liveboxandy/ZX-Interface-1-Replacement-ROM/Pictures/Original ROM Pins.jpg

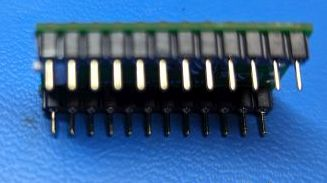
Pictures/Original ROM Pins.jpg
