liveboxandy/ZX-Interface-1-Replacement-ROM/Pictures/Programming.jpg

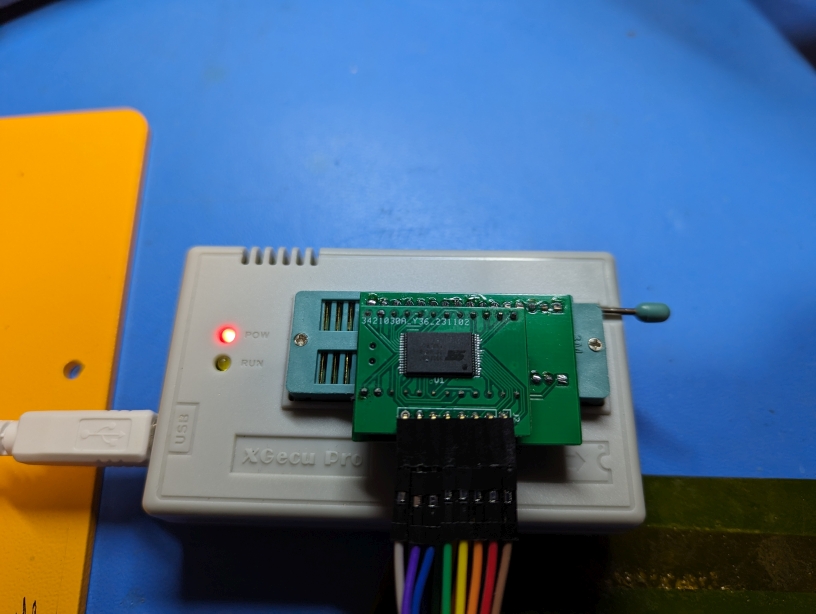
Pictures/Programming.jpg
