liveboxandy/ZX-Interface-1-Replacement-ROM/Pictures/ROM Bottom Offset.jpg

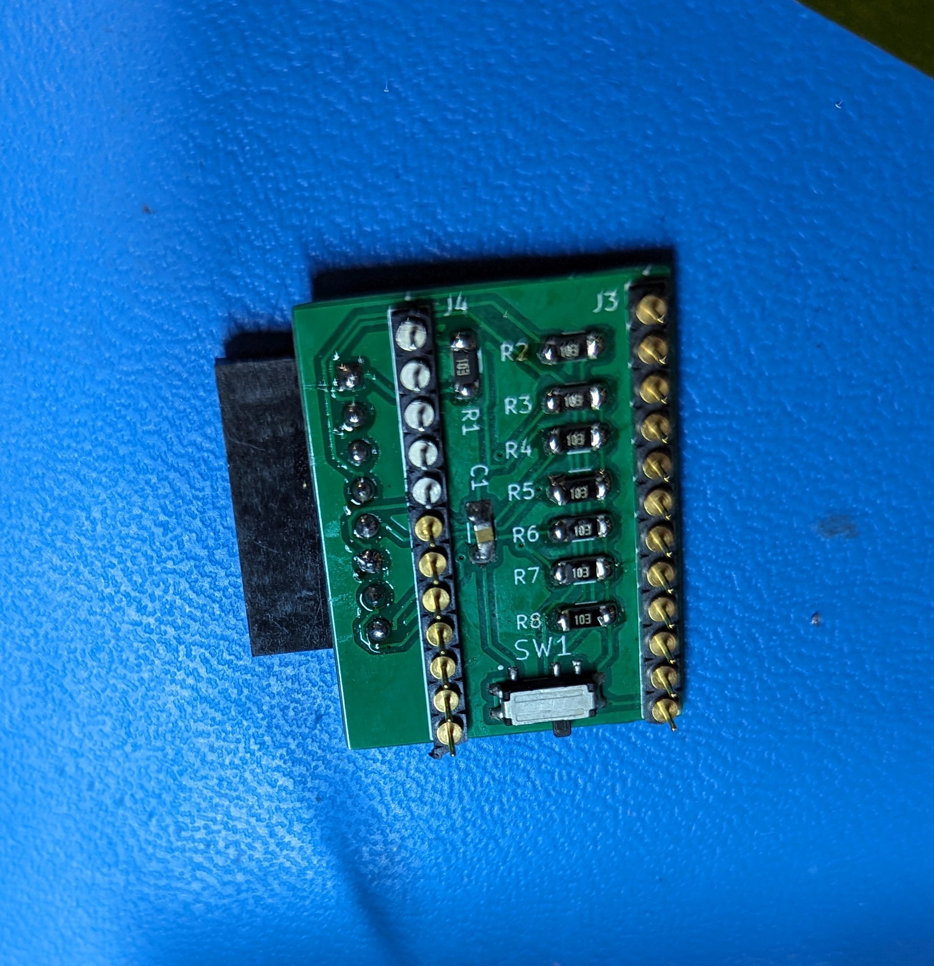
Pictures/ROM Bottom Offset.jpg
