liveboxandy/ZX-Interface-1-Replacement-ROM/Pictures/ROM In IF1 No Case.jpg

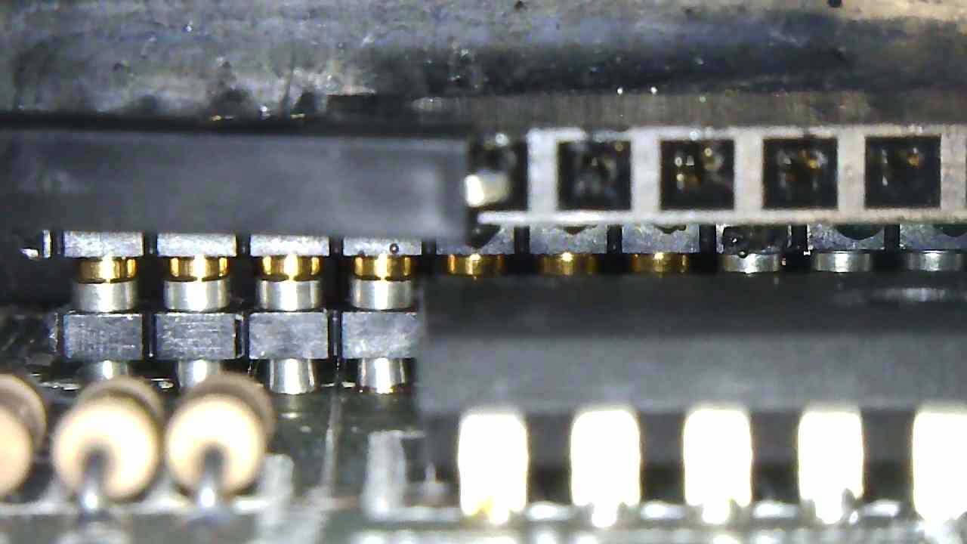
Pictures/ROM In IF1 No Case.jpg
