liveboxandy/ZX-Interface-1-Replacement-ROM/Pictures/ROM In Place.jpg

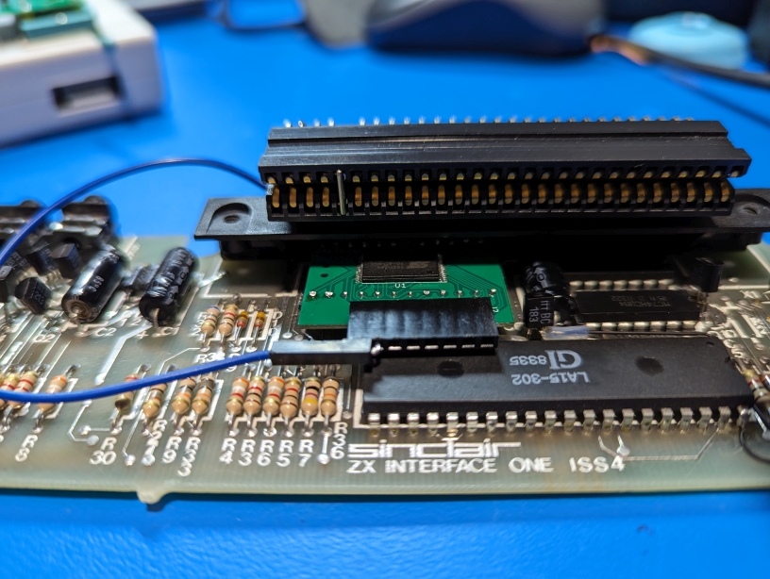
Pictures/ROM In Place.jpg
