liveboxandy/ZX-Interface-1-Replacement-ROM/Pictures/ROM Top Side.jpg

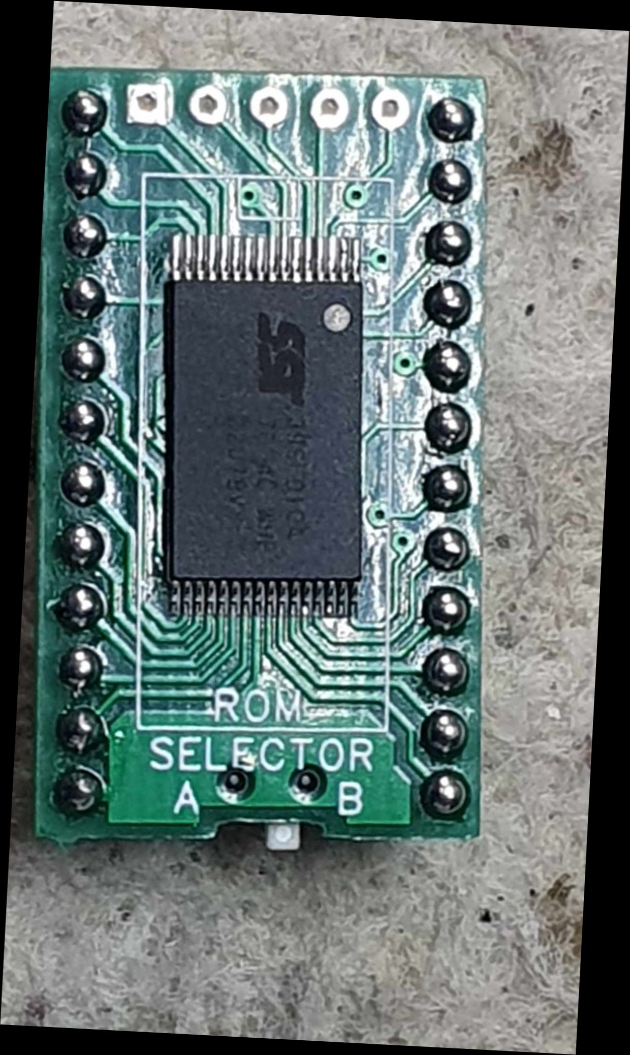
Pictures/ROM Top Side.jpg
