liveboxandy/ZX-Interface-1-Replacement-ROM/ZX Interface 1 ROM 39SF010.jpg

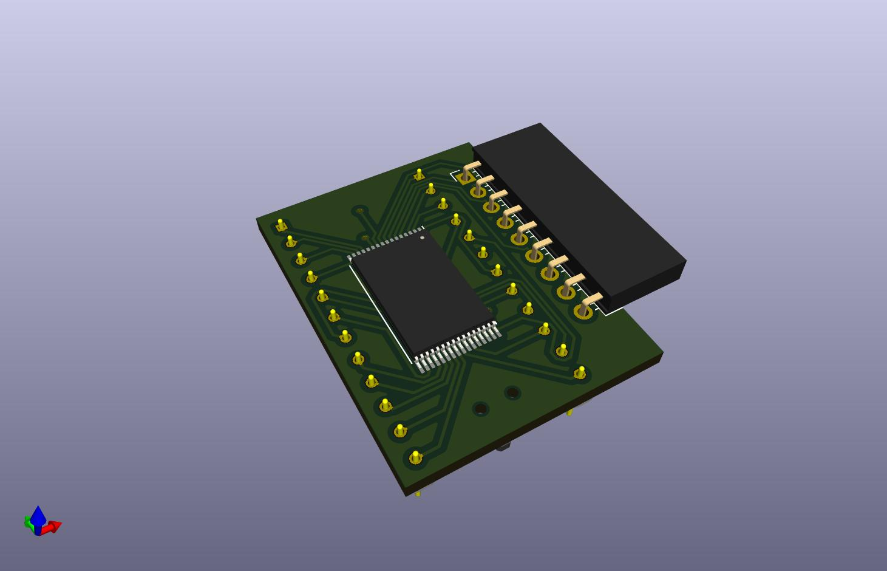
ZX Interface 1 ROM 39SF010.jpg
